janelia-idf/arduino_relay_remote_controller/pcb/arduino_relay_remote_controller.sch

## KiCad design pcb/arduino_relay_remote_controller.sch (2017-02-22)

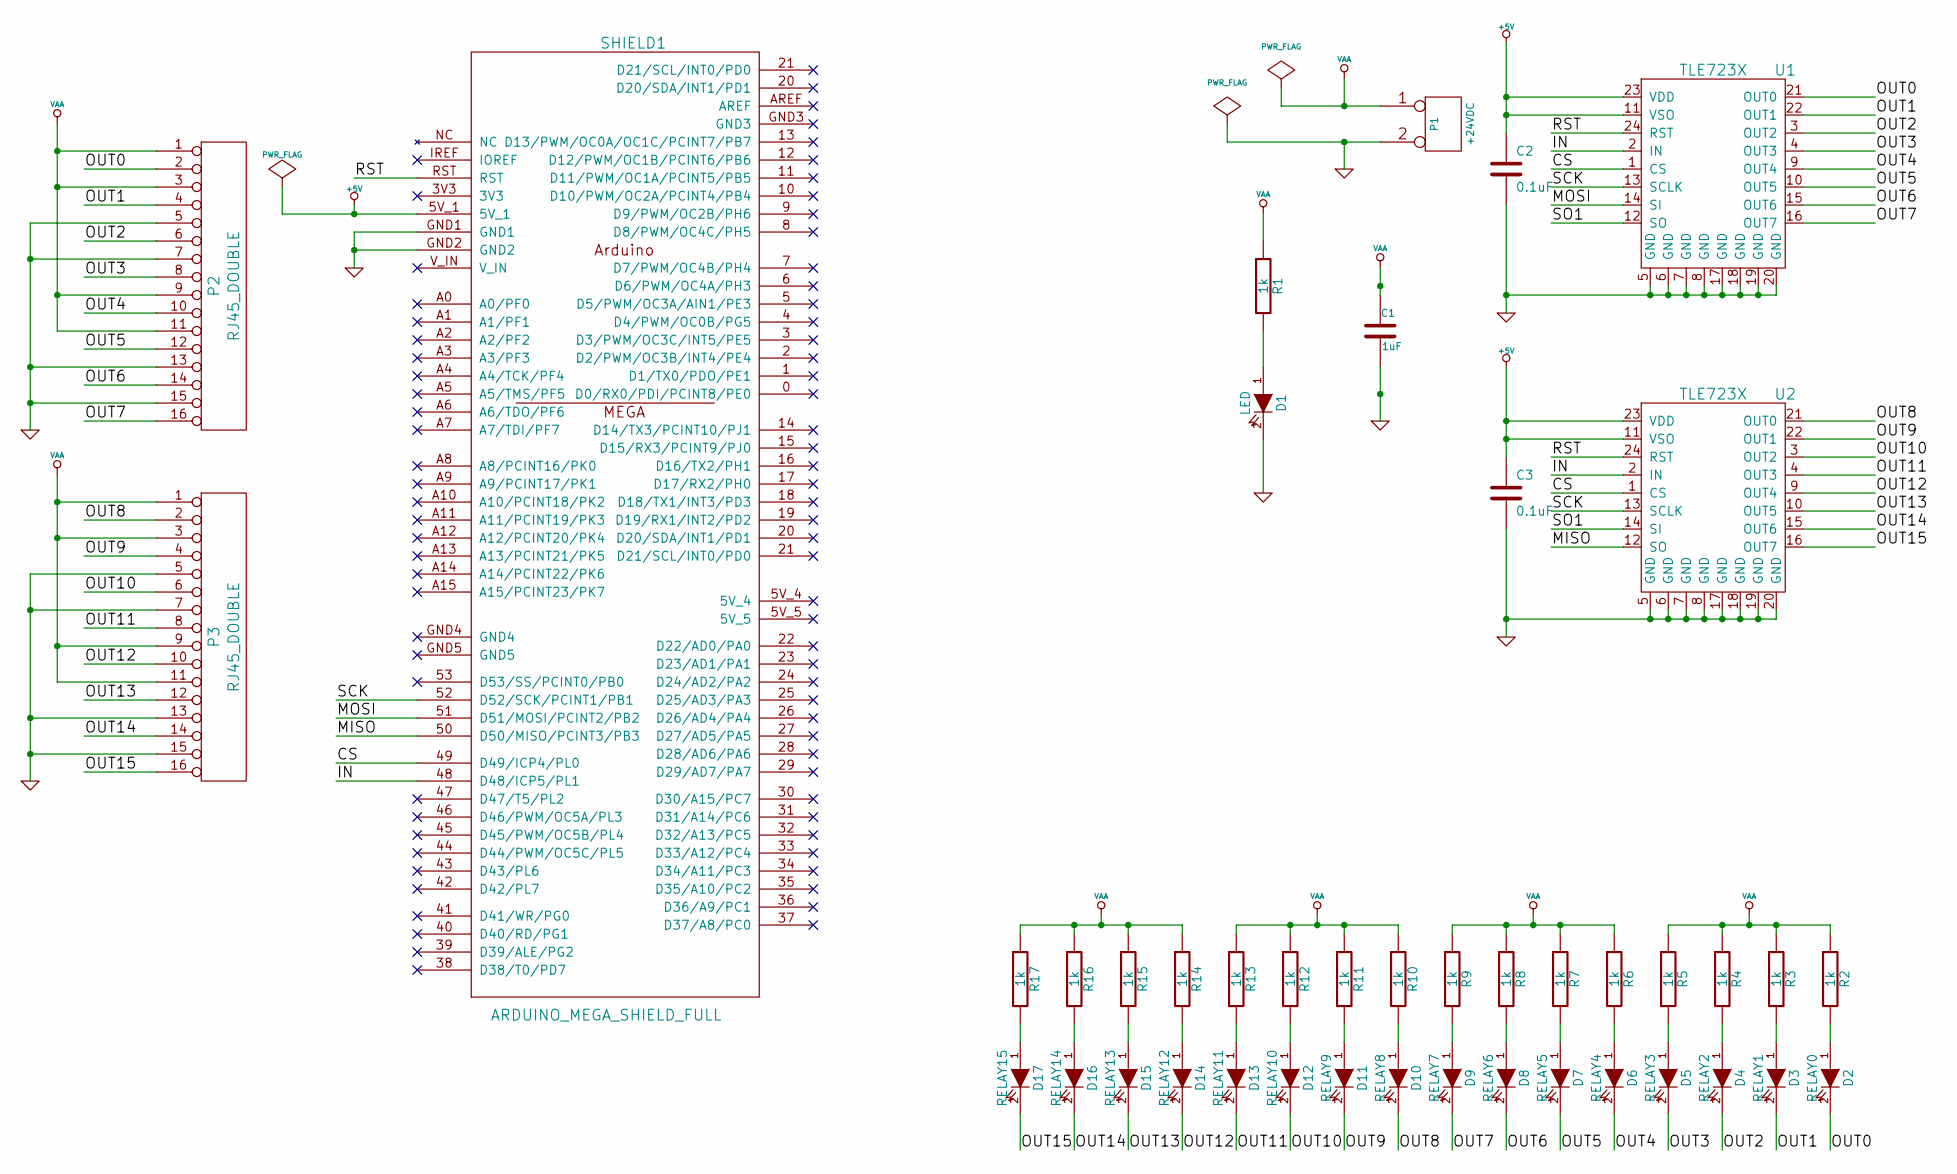
[picture p7: schematic arduino_relay_remote_controller.sch]

Parts:
C1: 1uF
C2, C3: 0.1uF
D1: LED
D2: RELAY0
D3: RELAY1
D4: RELAY2
D5: RELAY3
D6: RELAY4
D7: RELAY5
D8: RELAY6
D9: RELAY7
D10: RELAY8
D11: RELAY9
D12: RELAY10
D13: RELAY11
D14: RELAY12
D15: RELAY13
D16: RELAY14
D17: RELAY15
P1: +24VDC
P2, P3: RJ45_DOUBLE
R1, R2, R3, R4, R5, R6, R7, R8, R9, R10, R11, R12, R13, R14, R15, R16, R17: 1k
SHIELD1: ARDUINO_MEGA_SHIELD_FULL
U1, U2: TLE723X

Connections:
+5V: C2.1, C3.1, SHIELD1.5V_1, U1.11 (VSO), U1.23 (VDD), U2.11 (VSO), U2.23 (VDD)
CS: SHIELD1.49 (D49/ICP4/PL0), U1.1 (CS), U2.1 (CS)
GND: C1.2, C2.2, C3.2, D1.2 (K), P1.2 (PM), P2.5, P2.7, P2.13, P2.15, P3.5, P3.7, P3.13, P3.15, SHIELD1.GND1, SHIELD1.GND2, U1.5 (GND), U1.6 (GND), U1.7 (GND), U1.8 (GND), U1.17 (GND), U1.18 (GND), U1.19 (GND), U1.20 (GND), U2.5 (GND), U2.6 (GND), U2.7 (GND), U2.8 (GND), U2.17 (GND), U2.18 (GND), U2.19 (GND), U2.20 (GND)
IN: SHIELD1.48 (D48/ICP5/PL1), U1.2 (IN), U2.2 (IN)
MISO: SHIELD1.50 (D50/MISO/PCINT3/PB3), U2.12 (SO)
MOSI: SHIELD1.51 (D51/MOSI/PCINT2/PB2), U1.14 (SI)
unnamed: D1.1 (A), R1.2
unnamed: D2.1 (A), R2.2
unnamed: D3.1 (A), R3.2
unnamed: D4.1 (A), R4.2
unnamed: D5.1 (A), R5.2
unnamed: D6.1 (A), R6.2
unnamed: D7.1 (A), R7.2
unnamed: D8.1 (A), R8.2
unnamed: D9.1 (A), R9.2
unnamed: D10.1 (A), R10.2
unnamed: D11.1 (A), R11.2
unnamed: D12.1 (A), R12.2
unnamed: D13.1 (A), R13.2
unnamed: D14.1 (A), R14.2
unnamed: D15.1 (A), R15.2
unnamed: D16.1 (A), R16.2
unnamed: D17.1 (A), R17.2
OUT0: D2.2 (K), P2.2, U1.21 (OUT0)
OUT1: D3.2 (K), P2.4, U1.22 (OUT1)
OUT2: D4.2 (K), P2.6, U1.3 (OUT2)
OUT3: D5.2 (K), P2.8, U1.4 (OUT3)
OUT4: D6.2 (K), P2.10, U1.9 (OUT4)
OUT5: D7.2 (K), P2.12, U1.10 (OUT5)
OUT6: D8.2 (K), P2.14, U1.15 (OUT6)
OUT7: D9.2 (K), P2.16, U1.16 (OUT7)
OUT8: D10.2 (K), P3.2, U2.21 (OUT0)
OUT9: D11.2 (K), P3.4, U2.22 (OUT1)
OUT10: D12.2 (K), P3.6, U2.3 (OUT2)
OUT11: D13.2 (K), P3.8, U2.4 (OUT3)
OUT12: D14.2 (K), P3.10, U2.9 (OUT4)
OUT13: D15.2 (K), P3.12, U2.10 (OUT5)
OUT14: D16.2 (K), P3.14, U2.15 (OUT6)
OUT15: D17.2 (K), P3.16, U2.16 (OUT7)
RST: SHIELD1.RST, U1.24 (RST), U2.24 (RST)
SCK: SHIELD1.52 (D52/SCK/PCINT1/PB1), U1.13 (SCLK), U2.13 (SCLK)
SO1: U1.12 (SO), U2.14 (SI)
VAA: C1.1, P1.1, P2.1, P2.3, P2.9, P2.11, P3.1, P3.3, P3.9, P3.11, R1.1, R2.1, R3.1, R4.1, R5.1, R6.1, R7.1, R8.1, R9.1, R10.1, R11.1, R12.1, R13.1, R14.1, R15.1, R16.1, R17.1
